melisa204/proiect_tsc/Images/Screenshot 2025-04-06 at 20.56.31.png

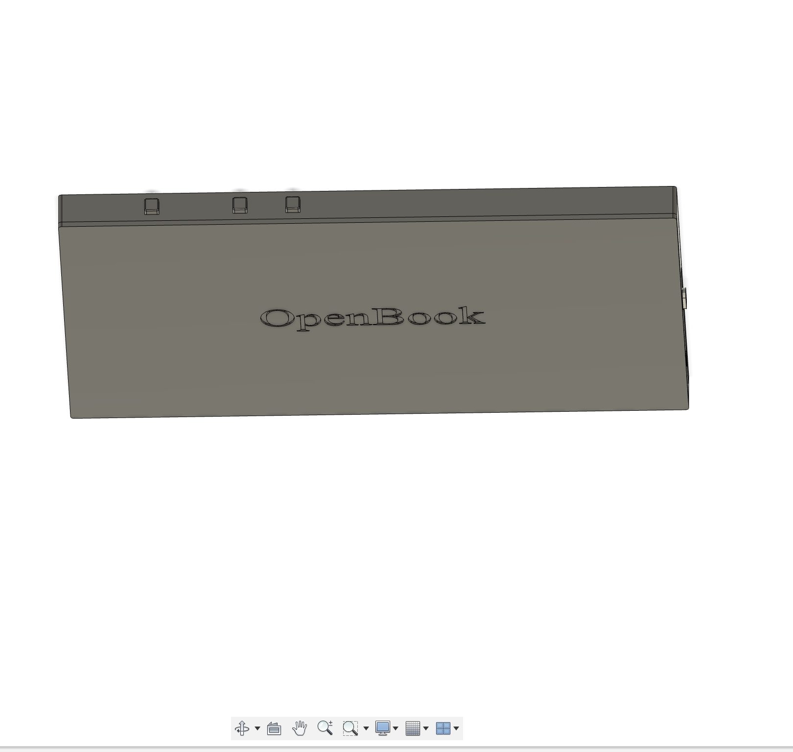
Images/Screenshot 2025-04-06 at 20.56.31.png
