melisa204/proiect_tsc/Images/Screenshot 2025-04-06 at 20.58.15.png

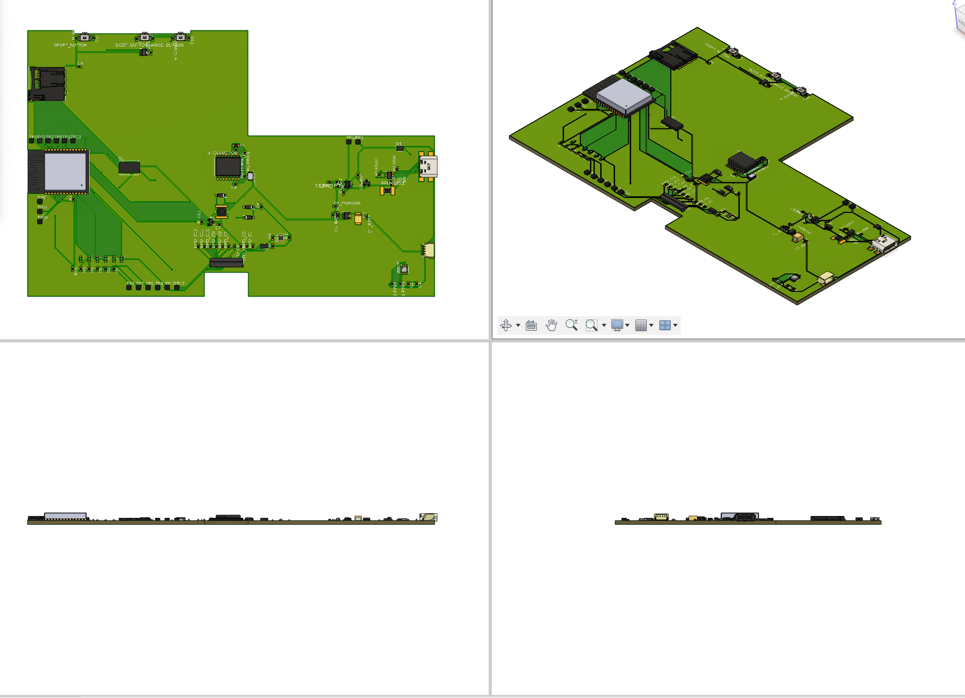
Images/Screenshot 2025-04-06 at 20.58.15.png
